zackgomez/i211ml-rack-mount/cad/devices-preview.png

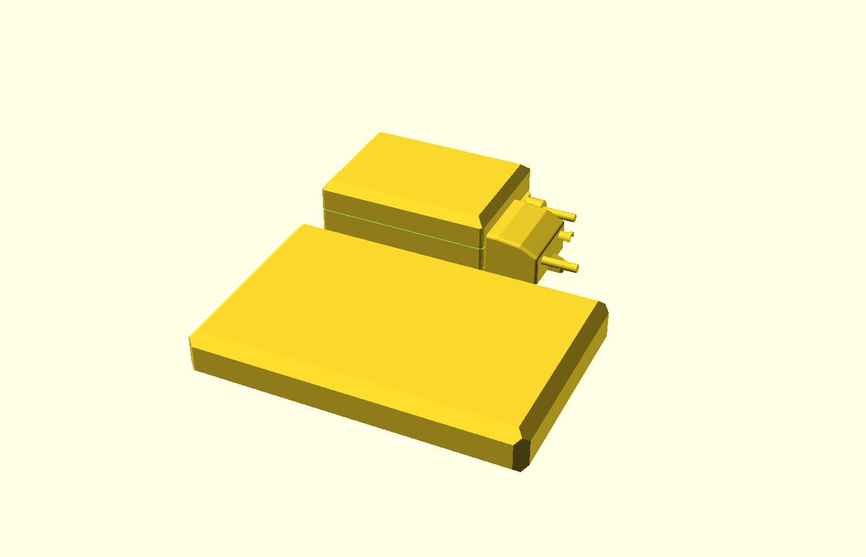
cad/devices-preview.png
