zackgomez/i211ml-rack-mount/cad/gauges-preview.png

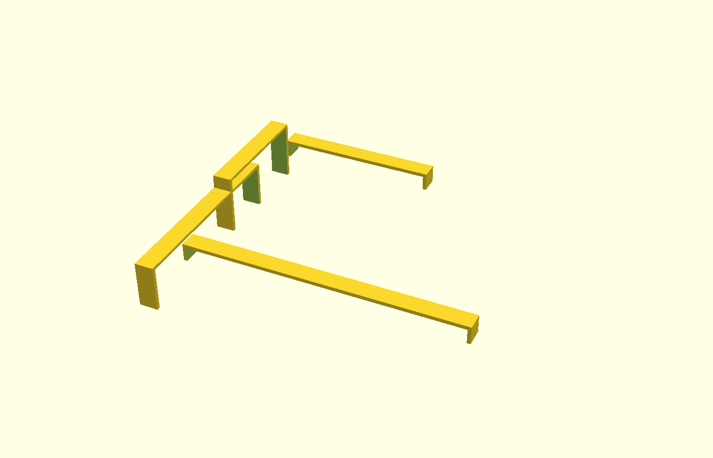
cad/gauges-preview.png
