zackgomez/i211ml-rack-mount/cad/mount-right-render.png

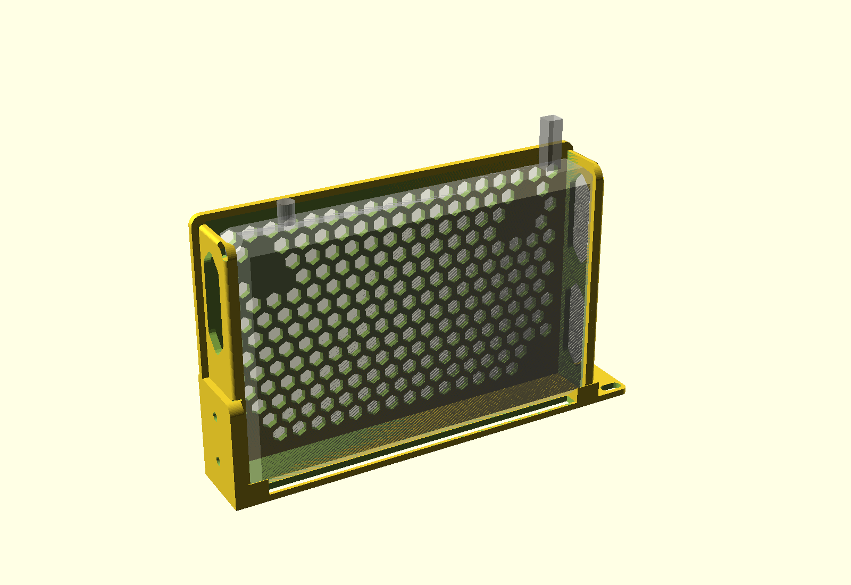
cad/mount-right-render.png
