zackgomez/i211ml-rack-mount/cad/render-left-iso.png

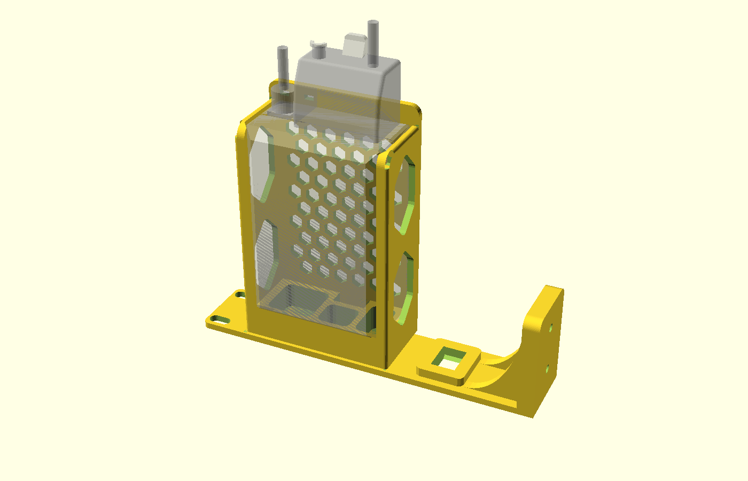
cad/render-left-iso.png
