zackgomez/i211ml-rack-mount/cad/render-right-iso.png

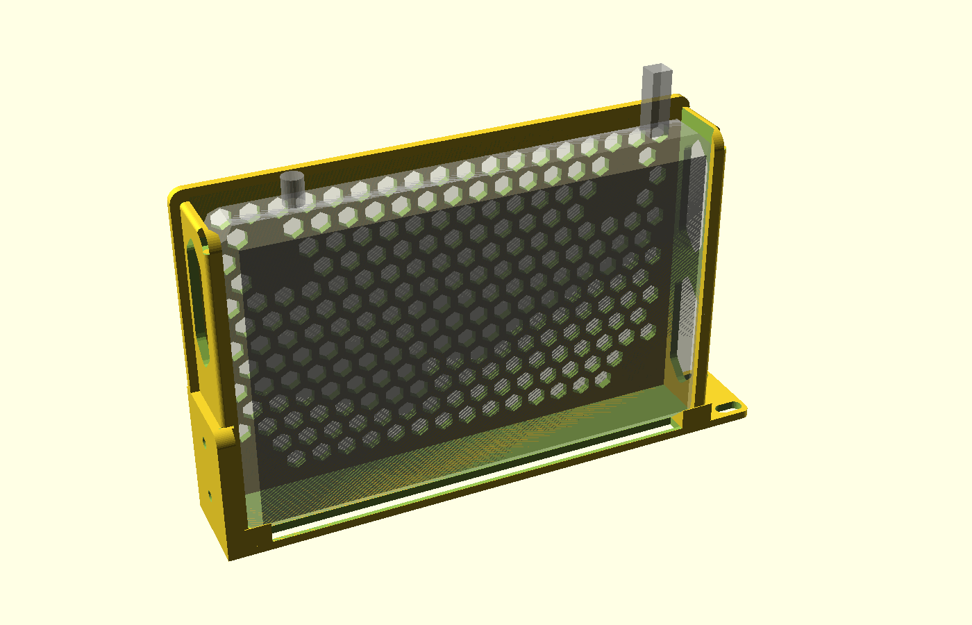
cad/render-right-iso.png
