zackgomez/i211ml-rack-mount/references/ebay-ont-i211ml-1.jpg

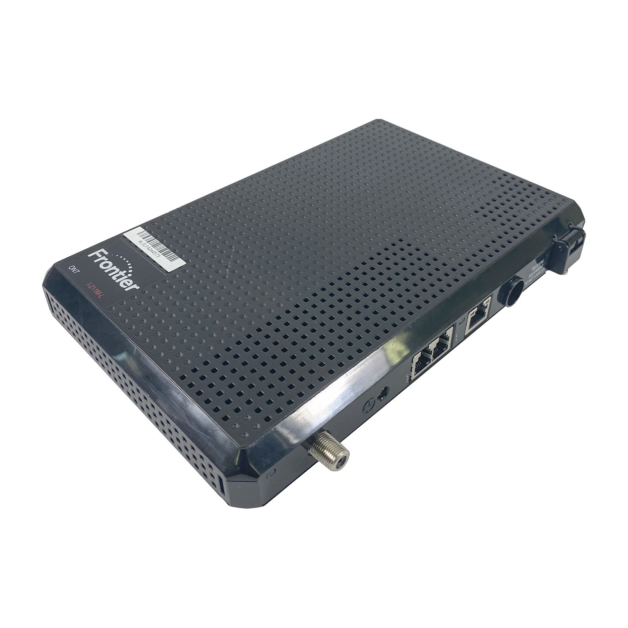
references/ebay-ont-i211ml-1.jpg
