zackgomez/i211ml-rack-mount/references/ebay-ont-i211ml-4.jpg

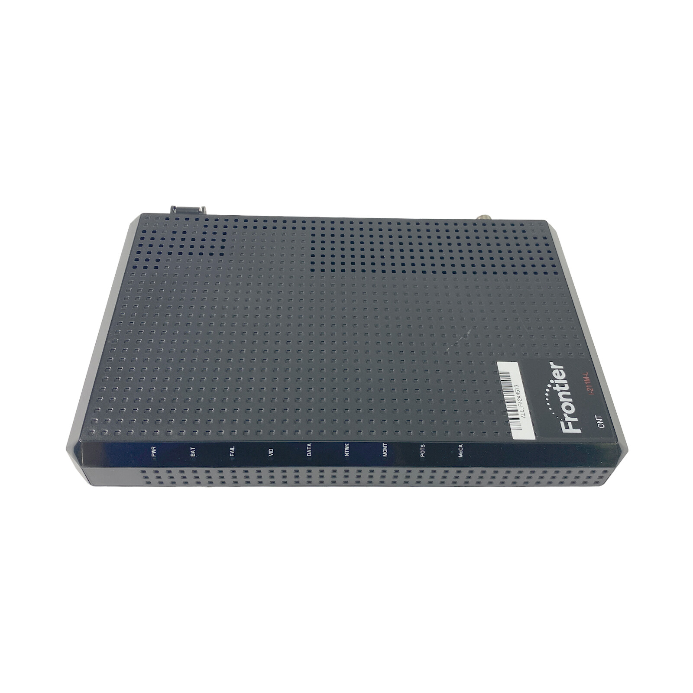
references/ebay-ont-i211ml-4.jpg
