zackgomez/i211ml-rack-mount/references/ebay-ont-i211ml-5.jpg

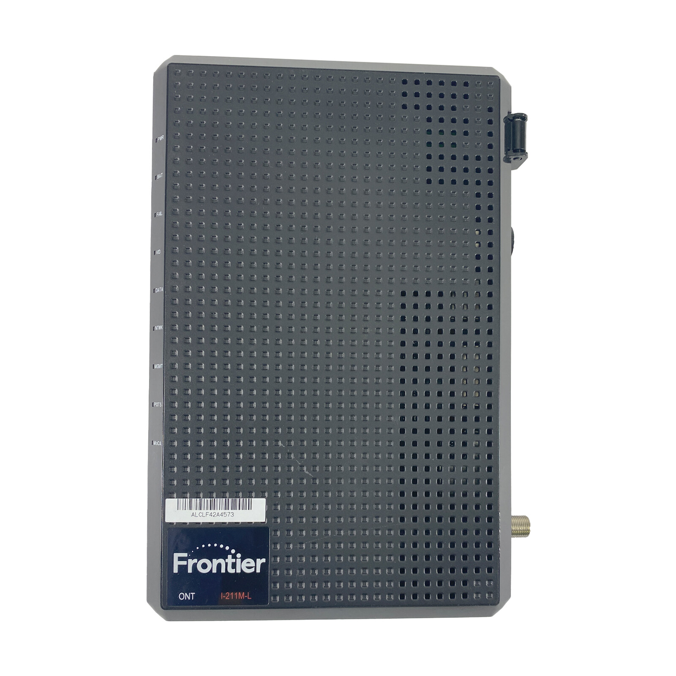
references/ebay-ont-i211ml-5.jpg
