zackgomez/i211ml-rack-mount/references/ebay-ont-i211ml-6.jpg

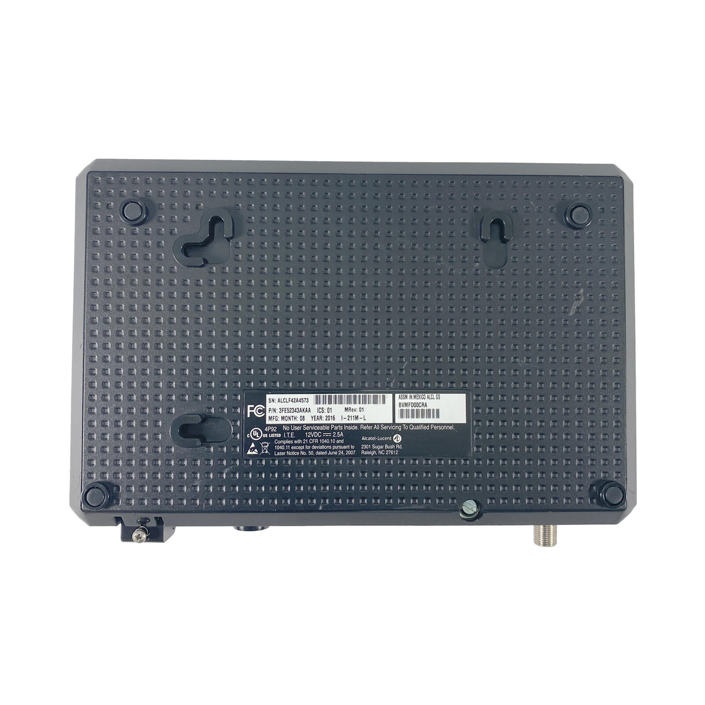
references/ebay-ont-i211ml-6.jpg
