zackgomez/i211ml-rack-mount/references/etsy-g211mc-mount-iso.png

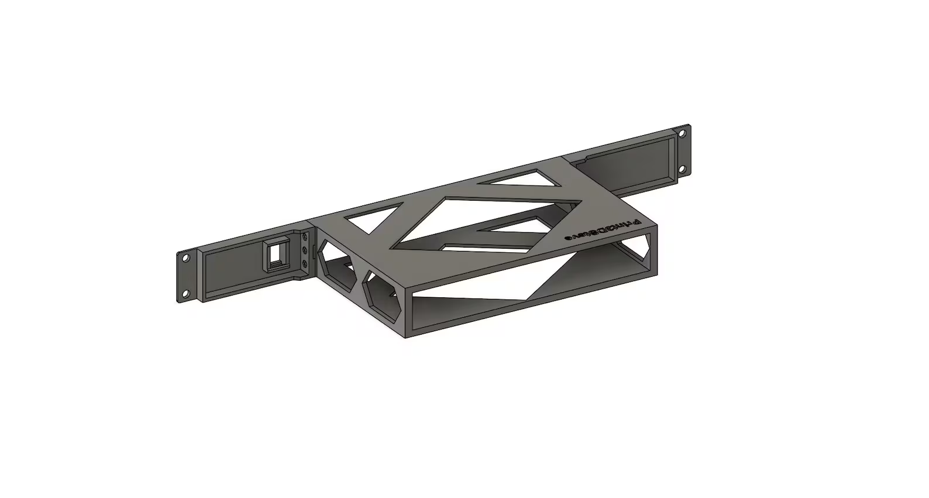
references/etsy-g211mc-mount-iso.png
