zackgomez/i211ml-rack-mount/cad/render-assembly-front.png

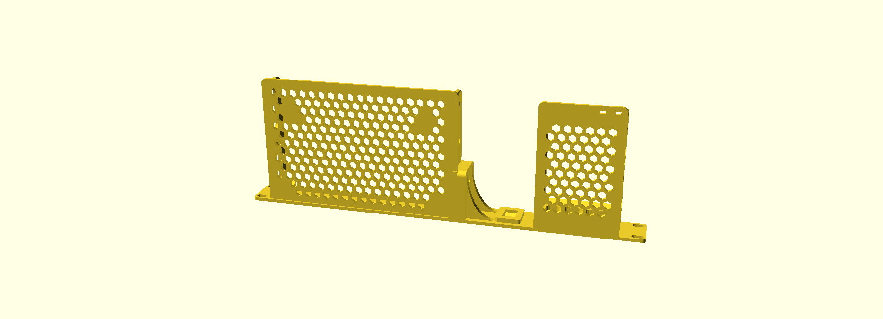
cad/render-assembly-front.png
